Parmenide/Afficheur-Led/Electronique/Kicad/Afficheur-Led [1:2]/Afficheur-Led-1:2.sch

## KiCad design Electronique/Kicad/Afficheur-Led [1:2]/Afficheur-Led-1:2.sch (2018-01-15)

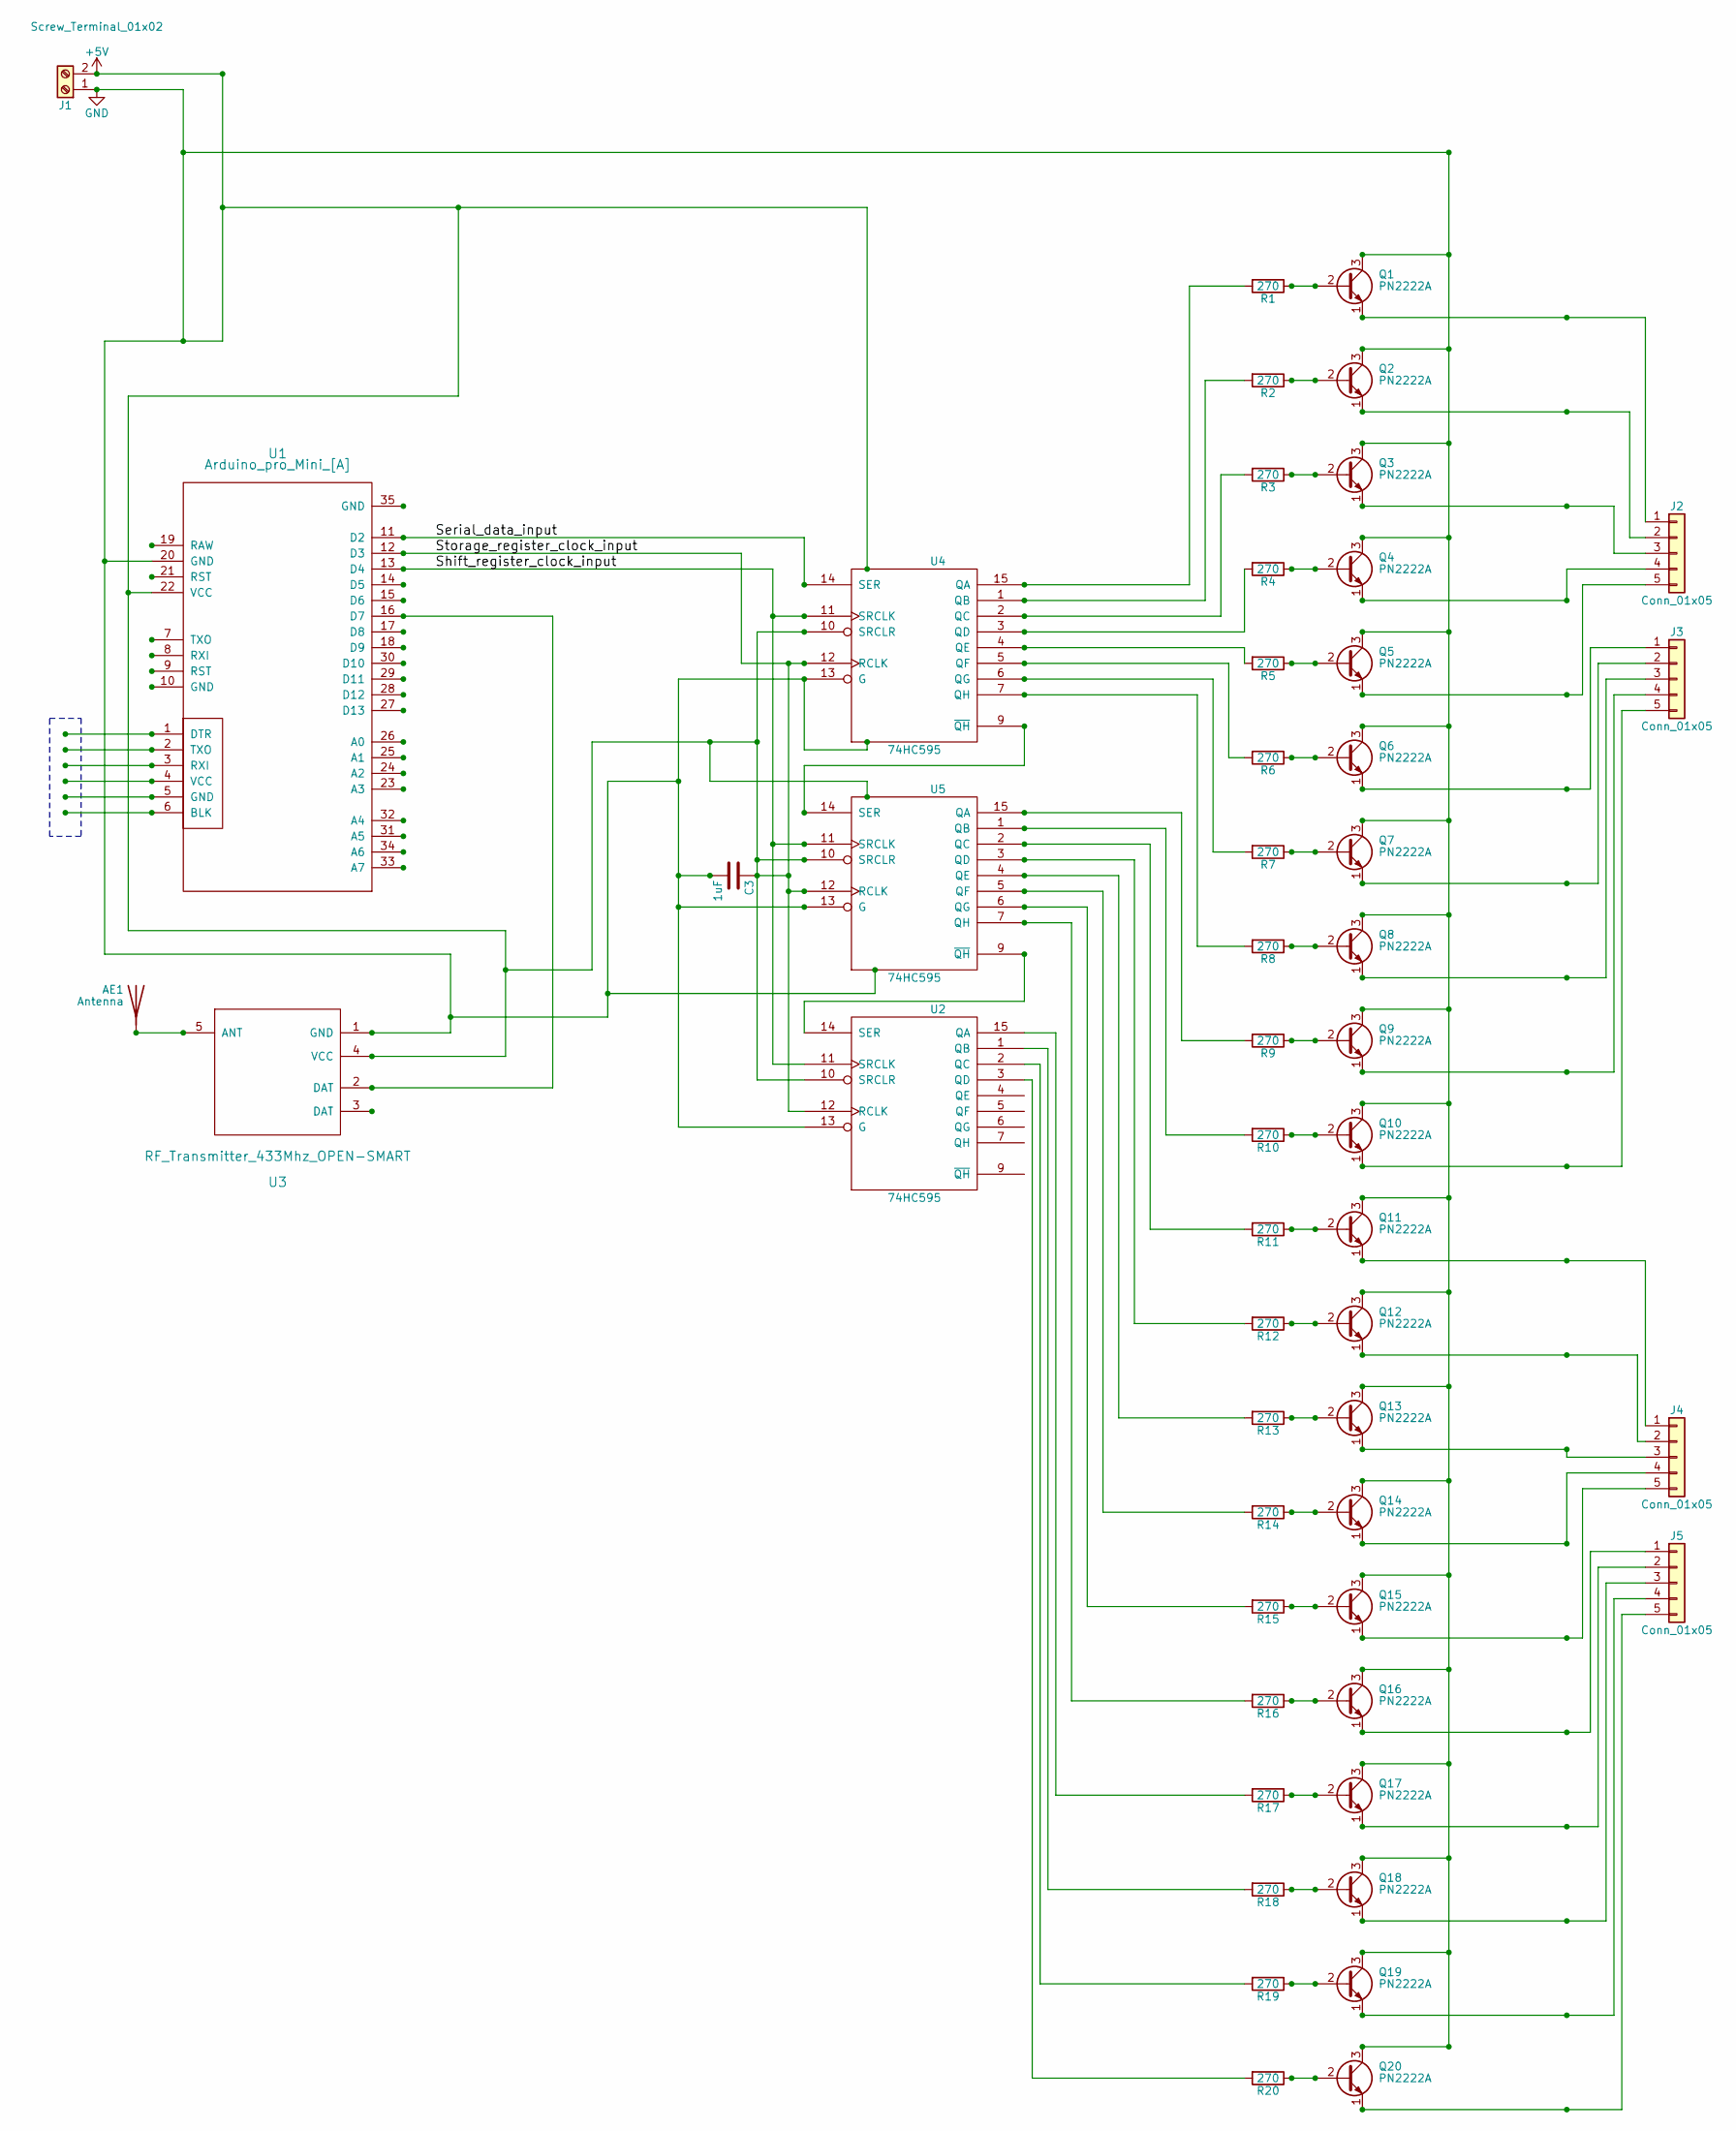
[picture p10: schematic Afficheur-Led-1:2.sch]

Parts:
AE1: Antenna; 1pin
C3: 1uF; C_Disc_D5.0mm_W2.5mm_P5.00mm
J1: Screw_Terminal_01x02; TerminalBlock_Pheonix_MPT-2.54mm_2pol
J2, J3, J4, J5: Conn_01x05; Pin_Header_Angled_1x05_Pitch2.54mm
Q1, Q2, Q3, Q4, Q5, Q6, Q7, Q8, Q9, Q10, Q11, Q12, Q13, Q14, Q15, Q16, Q17, Q18, Q19, Q20: PN2222A; TO-92_Inline_Wide
R1, R2, R3, R4, R5, R6, R7, R8, R9, R10, R11, R12, R13, R14, R15, R16, R17, R18, R19, R20: 270; R_Axial_DIN0207_L6.3mm_D2.5mm_P10.16mm_Horizontal
U1: Arduino_pro_Mini_[A]; Arduino-Pro-Mini
U2, U4, U5: 74HC595; DIP-16_W7.62mm
U3: RF_Transmitter_433Mhz_OPEN-SMART; RF-440mhz-Receiver

Connections:
+5V: C3.1, C3.2, J1.1, J1.2, Q1.3 (C), Q2.3 (C), Q3.3 (C), Q4.3 (C), Q5.3 (C), Q6.3 (C), Q7.3 (C), Q8.3 (C), Q9.3 (C), Q10.3 (C), Q11.3 (C), Q12.3 (C), Q13.3 (C), Q14.3 (C), Q15.3 (C), Q16.3 (C), Q17.3 (C), Q18.3 (C), Q19.3 (C), Q20.3 (C), U1.12 (D3), U1.20 (GND), U1.22 (VCC), U2.10 (SRCLR), U2.12 (RCLK), U2.13 (G), U3.1 (GND), U3.4 (VCC), U4.8 (GND), U4.10 (SRCLR), U4.12 (RCLK), U4.13 (G), U4.16 (VCC), U5.10 (SRCLR), U5.12 (RCLK), U5.13 (G), U5.16 (VCC)
unnamed: AE1.1, U3.5 (ANT)
unnamed: J2.1, Q1.1 (E)
unnamed: J2.2, Q2.1 (E)
unnamed: J2.3, Q3.1 (E)
unnamed: J2.4, Q4.1 (E)
unnamed: J2.5, Q5.1 (E)
unnamed: J3.1, Q6.1 (E)
unnamed: J3.2, Q7.1 (E)
unnamed: J3.3, Q8.1 (E)
unnamed: J3.4, Q9.1 (E)
unnamed: J3.5, Q10.1 (E)
unnamed: J4.1, Q11.1 (E)
unnamed: J4.2, Q12.1 (E)
unnamed: J4.3, Q13.1 (E)
unnamed: J4.4, Q14.1 (E)
unnamed: J4.5, Q15.1 (E)
unnamed: J5.1, Q16.1 (E)
unnamed: J5.2, Q17.1 (E)
unnamed: J5.3, Q18.1 (E)
unnamed: J5.4, Q19.1 (E)
unnamed: J5.5, Q20.1 (E)
unnamed: Q1.2 (B), R1.1
unnamed: Q2.2 (B), R2.1
unnamed: Q3.2 (B), R3.1
unnamed: Q4.2 (B), R4.1
unnamed: Q5.2 (B), R5.1
unnamed: Q6.2 (B), R6.1
unnamed: Q7.2 (B), R7.1
unnamed: Q8.2 (B), R8.1
unnamed: Q9.2 (B), R9.1
unnamed: Q10.2 (B), R10.1
unnamed: Q11.2 (B), R11.1
unnamed: Q12.2 (B), R12.1
unnamed: Q13.2 (B), R13.1
unnamed: Q14.2 (B), R14.1
unnamed: Q15.2 (B), R15.1
unnamed: Q16.2 (B), R16.1
unnamed: Q17.2 (B), R17.1
unnamed: Q18.2 (B), R18.1
unnamed: Q19.2 (B), R19.1
unnamed: Q20.2 (B), R20.1
unnamed: R1.2, U4.15 (QA)
unnamed: R2.2, U4.1 (QB)
unnamed: R3.2, U4.2 (QC)
unnamed: R4.2, U4.3 (QD)
unnamed: R5.2, U4.4 (QE)
unnamed: R6.2, U4.5 (QF)
unnamed: R7.2, U4.6 (QG)
unnamed: R8.2, U4.7 (QH)
unnamed: R9.2, U5.15 (QA)
unnamed: R10.2, U5.1 (QB)
unnamed: R11.2, U5.2 (QC)
unnamed: R12.2, U5.3 (QD)
unnamed: R13.2, U5.4 (QE)
unnamed: R14.2, U5.5 (QF)
unnamed: R15.2, U5.6 (QG)
unnamed: R16.2, U5.7 (QH)
unnamed: R17.2, U2.15 (QA)
unnamed: R18.2, U2.1 (QB)
unnamed: R19.2, U2.2 (QC)
unnamed: R20.2, U2.3 (QD)
unnamed: U1.16 (D7), U3.2 (DAT)
unnamed: U2.14 (SER), U5.9 (~QH)
unnamed: U4.9 (~QH), U5.14 (SER)
Serial_data_input: U1.11 (D2), U4.14 (SER)
Shift_register_clock_input: U1.13 (D4), U2.11 (SRCLK), U4.11 (SRCLK), U5.11 (SRCLK)
