Parmenide/Afficheur-Led/Electronique/Kicad/Afficheur-Led [2:2]/Afficheur-Led-2:2.sch

## KiCad design Electronique/Kicad/Afficheur-Led [2:2]/Afficheur-Led-2:2.sch (2018-01-15)

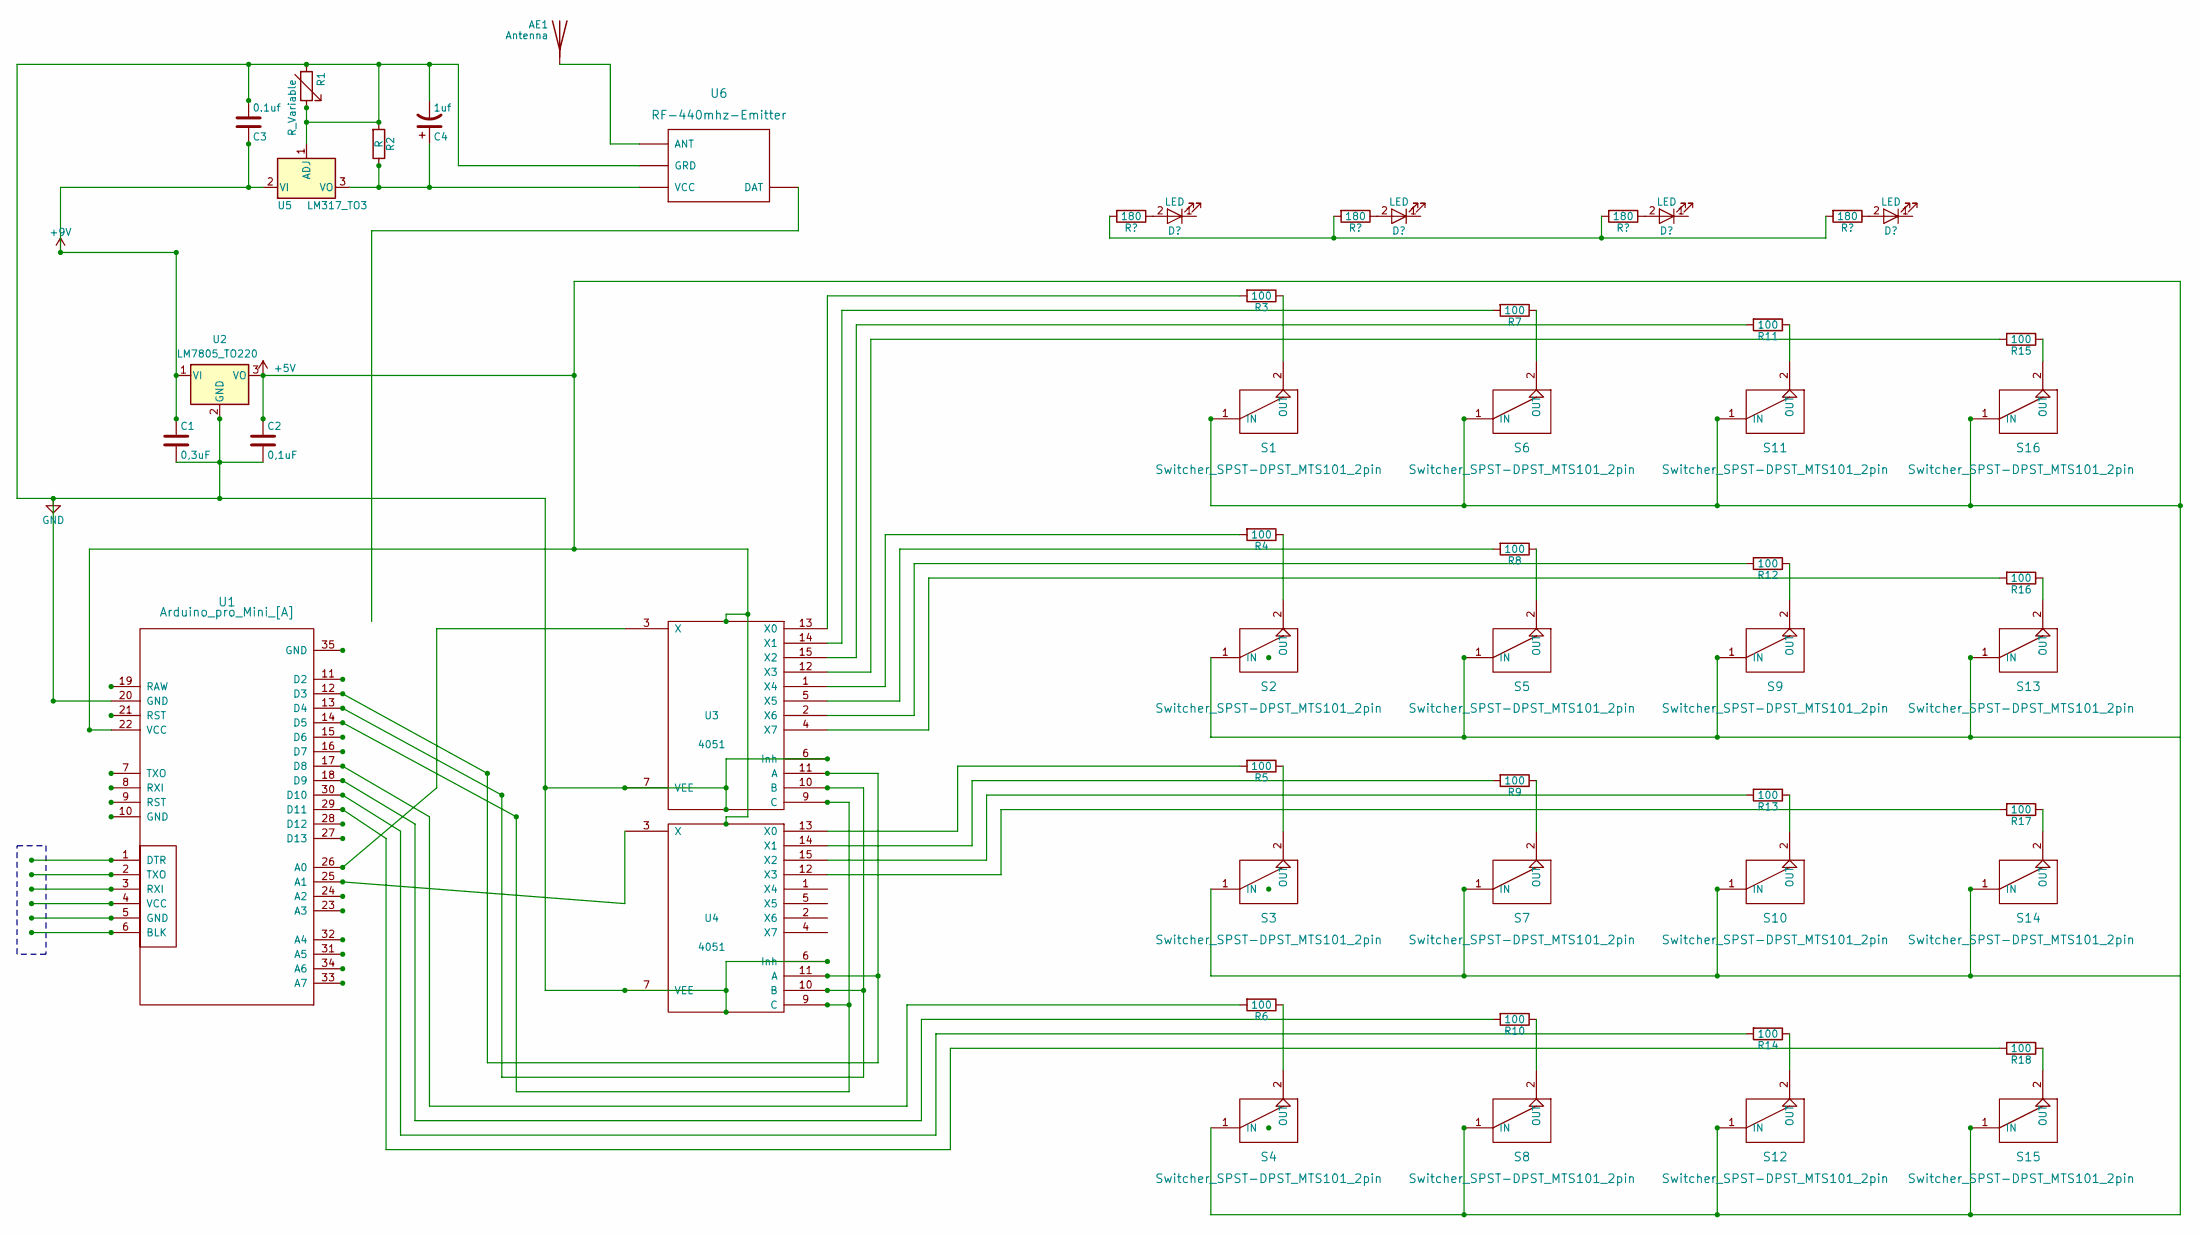
[picture p11: schematic Afficheur-Led-2:2.sch]

Parts:
AE1: Antenna; 1pin
C1: 0,3uF; C_Disc_D5.0mm_W2.5mm_P5.00mm
C2: 0,1uF; C_Disc_D5.0mm_W2.5mm_P5.00mm
C3: 0.1uf; C_Disc_D5.0mm_W2.5mm_P5.00mm
C4: 1uf; CP_Radial_D5.0mm_P2.50mm
R1: R_Variable; Potentiometer_Triwood_RM-065
R2: R; R_Axial_DIN0411_L9.9mm_D3.6mm_P15.24mm_Horizontal
R3, R4, R5, R6, R7, R8, R9, R10, R11, R12, R13, R14, R15, R16, R17, R18: 100
S1, S2, S3, S4, S5, S6, S7, S8, S9, S10, S11, S12, S13, S14, S15, S16: Switcher_SPST-DPST_MTS101_2pin
U1: Arduino_pro_Mini_[A]; Arduino-Pro-Mini
U2: LM7805_TO220; TO-220-3_Vertical
U3, U4: 4051
U5: LM317_TO3; TO-3
U6: RF-440mhz-Emitter

Connections:
+5V: C2.1, S1.1 (IN), S4.1 (IN), S6.1 (IN), S8.1 (IN), S11.1 (IN), S12.1 (IN), S15.1 (IN), S16.1 (IN), U1.22 (VCC), U2.3 (VO), U3.16 (VDD), U4.16 (VDD)
+9V: C1.1, C3.1, U2.1 (VI), U5.2 (VI)
GND: C1.2, C2.2, C3.2, C4.2, R1.1, R1.2, R2.2, U1.20 (GND), U2.2 (GND), U3.6 (Inh), U3.7 (VEE), U3.8 (VSS), U4.6 (Inh), U4.7 (VEE), U4.8 (VSS), U5.1 (ADJ), U6.~
unnamed: AE1.1, U6.~
unnamed: C4.1, R2.1, U5.3 (VO), U6.~
unnamed: R3.1, S1.2 (OUT)
unnamed: R3.2, U3.13 (X0)
unnamed: R4.1, S2.2 (OUT)
unnamed: R4.2, U3.1 (X4)
unnamed: R5.1, S3.2 (OUT)
unnamed: R5.2, U4.13 (X0)
unnamed: R6.1, S4.2 (OUT)
unnamed: R6.2, U1.17 (D8)
unnamed: R7.1, S6.2 (OUT)
unnamed: R7.2, U3.14 (X1)
unnamed: R8.1, S5.2 (OUT)
unnamed: R8.2, U3.5 (X5)
unnamed: R9.1, S7.2 (OUT)
unnamed: R9.2, U4.14 (X1)
unnamed: R10.1, S8.2 (OUT)
unnamed: R10.2, U1.18 (D9)
unnamed: R11.1, S11.2 (OUT)
unnamed: R11.2, U3.15 (X2)
unnamed: R12.1, S9.2 (OUT)
unnamed: R12.2, U3.2 (X6)
unnamed: R13.1, S10.2 (OUT)
unnamed: R13.2, U4.15 (X2)
unnamed: R14.1, S12.2 (OUT)
unnamed: R14.2, U1.30 (D10)
unnamed: R15.1, S16.2 (OUT)
unnamed: R15.2, U3.12 (X3)
unnamed: R16.1, S13.2 (OUT)
unnamed: R16.2, U3.4 (X7)
unnamed: R17.1, S14.2 (OUT)
unnamed: R17.2, U4.12 (X3)
unnamed: R18.1, S15.2 (OUT)
unnamed: R18.2, U1.29 (D11)
unnamed: S3.1 (IN), S7.1 (IN), S10.1 (IN), S14.1 (IN)
unnamed: S2.1 (IN), S5.1 (IN), S9.1 (IN), S13.1 (IN)
unnamed: U1.12 (D3), U3.11 (A), U4.11 (A)
unnamed: U1.13 (D4), U3.10 (B), U4.10 (B)
unnamed: U1.14 (D5), U3.9 (C), U4.9 (C)
unnamed: U1.25 (A1), U4.3 (X)
unnamed: U1.26 (A0), U3.3 (X)
